VID-PRO/BambuTagger-AMS-C/src/secrets_template.h

#ifndef SECRETS_H
#define SECRETS_H
// Copy this file to secrets.h and fill in your details.
// This file is a template and should NOT be committed to version control.

// WiFi credentials can be configured via the web interface instead.
// If you prefer hardcoding, rename this file to secrets.h and fill in:

#define SECRET_WIFI_SSID     ""
#define SECRET_WIFI_PASSWORD ""

// Optional: pre-configure printer connection
#define SECRET_PRINTER_IP       "192.168.1.100"
#define SECRET_PRINTER_PORT     8883
#define SECRET_PRINTER_ACCESS   ""
#define SECRET_PRINTER_SERIAL   ""

#endif
